jtxi123/CaeliA-Device/CaeliA_Device/CaeliA_DeviceLP08V14/root_ca.h

const char* /*github_*/root_ca = R"ROOT_CA(
-----BEGIN CERTIFICATE-----
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
-----END CERTIFICATE-----
)ROOT_CA";
